Zeren/Automobile-PMR/LTspice/Input_mic_amplifier.asc

C1: cap; 10µ
C2: cap; 10µ
C3: cap; 10n
C4: cap; 10µ
C5: cap; 1n
C6: cap; 10n
C7: cap; 10n
C8: cap; 100n
R1: res; 1k
R2: res; 1k
R3: res; 10k
R4: res; 10k
R5: res; 10k
R6: res; 10k
R7: res; 10k
R8: res; 47k
R9: res; 47k
R10: res; 4.7k
R11: res; 4k7
R12: res; 4k7
R13: res; 4k7
R14: res; 4k7
R15: res; 47
U1: NE5532
U2: NE5532
U3: NE5532
V1: voltage; 15
V2: voltage; 7.5
V3: voltage; 0; AC 1; Rser=100
Named nets: 0, V+, REF, out
.ac dec 100 1 100meg
