Zeren/Automobile-PMR/LTspice/5x multiplier.asc

C1: cap; 10p
C2: cap; 1n
C3: cap; 12.734p
D1: schottky; RB715UM
L1: ind2; 318.354n
L2: ind2; 10n; Rser=0.1
R3: res; 1k
V1: voltage; PULSE(0 3.3 0 1n 1n 5.6053n 11.21n)
V2: voltage; 5; Rser=0
V3: voltage; SINE(1.65 1.65 89.2meg); AC 1; Rser=0
Named nets: 0
;ac dec 100 10meg 1g
.tran 1u
