Zeren/Automobile-PMR/LTspice/FM detector.asc

C1: cap; 100p
C2: cap; 120p
L1: ind; 1µ; Rser=1
R1: res; 10k
V1: voltage; SFFM(0 1 10.7meg 2 1k); AC 1
Named nets: 0, in, out
.tran 2m
