Zeren/Automobile-PMR/LTspice/AF amp.asc

C1: cap; 10n
C2: cap; 10.5n
C3: cap; 10n
C4: cap; 10.5n
C5: cap; 1µ
R1: res; 2.2k
R2: res; 9.1k
R3: res; 3k
R4: res; 2.4k
R5: res; 4.3k
R6: res; 4.7k
R7: res; 3k
R8: res; 2.4k
R9: res; 10k
U1: NE5532
U2: NE5532
V1: voltage; 5
V2: voltage; -5
V3: voltage; 1.6; AC 1
Named nets: v+, v-, 0, out
.ac dec 100 10 10meg
