Zeren/Automobile-PMR/LTspice/AGC detector.asc

C1: cap; 10n
C2: cap; 10n
C3: cap; 100n
D1: schottky; BAS40HM
L1: ind; 100µ
R1: res; 1800
R2: res; 50
R3: res; 50
R4: res; 10k
R5: res; 4k7
R6: res; 10k
R7: res; 10k
U1: LT1002
U2: LT1002
V1: voltage; SINE(0 0.5 10.7meg); AC 1
V2: voltage; 5
V3: voltage; -5
Named nets: 0, agc_out, rf_out, rf_in, det, tru, V+, V-
.tran 0 5m 4m
