Zeren/Automobile-PMR/LTspice/IF2 filter a amp.asc

C1: cap; 10n
C2: cap; 10n
C3: cap; 1n
C4: cap; 10n
C5: cap; 1µ
C6: cap; 1µ
C7: cap; 100n
R1: res; 10K
R2: res; 10K
R3: res; 50
R4: res; 10
R5: res; 100
R6: res; 10K
R7: res; 10K
R8: res; 10k
R9: res; 1k
R10: res; 1k
R11: res; 68k
U1: LM324
U2: LM324
U3: LM324
U5: LT1720
V1: voltage; 5
V2: voltage; -5
V3: voltage; SINE(0 2.23 100k); AC 1; Rser=50
V4: voltage; 1.6
V5: voltage; 3.3
Named nets: 0, V+, V-, in, out, REF
.tran 0.5m
;ac dec 100 1 100MEG
