Zeren/Automobile-PMR/Software/PMR_for_R124_V2/Core/Inc/rda1846.h

#ifndef RDA1846_H
#define RDA1846_H

#include "stm32g0xx_hal.h"

// I2C 7-bitová adresa (při SEN = Low)
#define RDA1846_I2C_ADDR  0x71

// Paging konstanty (stránkování nadadresových registrů)
#define RDA1846_PAGE_REG   0x7F
#define RDA1846_PAGE_UP    0x0001
#define RDA1846_PAGE_DOWN  0x0000
#define RDA1846_ADDR_LIMIT 0x80

// Využití unionu a bitfields pro bezpečnější přístup k registru 0x30
typedef union {
    uint16_t value;
    struct {
        uint16_t soft_reset   : 1;  // Bit 0
        uint16_t chip_cal_en  : 1;  // Bit 1
        uint16_t pdn_reg      : 1;  // Bit 2
        uint16_t sq_on        : 1;  // Bit 3
        uint16_t vox_on       : 1;  // Bit 4
        uint16_t rx_on        : 1;  // Bit 5
        uint16_t tx_on        : 1;  // Bit 6
        uint16_t mute         : 1;  // Bit 7
        uint16_t st_mode      : 2;  // Bity 9:8
        uint16_t reserved     : 1;  // Bit 10
        uint16_t tail_elim_en : 1;  // Bit 11
        uint16_t channel_mode : 2;  // Bity 13:12
        uint16_t others       : 2;  // Bity 15:14
    } bits;
} RDA1846_Reg30_t;

typedef struct {
    uint16_t tx_CTCSS;
    uint16_t rx_CTCSS;
    uint16_t tone;
} RDA1846_ctcss;

// RF Band Options
#define RDA1846_BAND_REG 0x0F
#define RDA1846_BAND_400_520MHZ  0x00
#define RDA1846_BAND_200_260MHZ  0x02
#define RDA1846_BAND_134_174MHZ  0x03

// Frequency setting
#define RDA1846_FREQ_HIGH_VALUE 0x29
#define RDA1846_FREQ_LOW_VALUE 0x2A

// Reference Clock Mode
#define RDA1846_CLOCK_XTAL_REG 0x2B
#define RDA1846_CLOCK_ADCLK_REG 0x2C
#define RDA1846_CLOCK_MODE_REG 0x04
#define RDA1846_CLOCK_MODE_12_14MHZ 0x0001
#define RDA1846_CLOCK_MODE_24_28MHZ 0x0000

//Deep sleep
#define RDA1846_DEEP_SLEEP_ENABLE 0x0004
#define RDA1846_DEEP_SLEEP_DISABLE 0x0000

//TX voice channel
#define RDA1846_TX_VOICE_CHANNEL_REG 0x3C
#define RDA1846_TX_VOICE_CHANNEL_MIC 0x0000
#define RDA1846_TX_VOICE_CHANNEL_TONE 0x4000
#define RDA1846_TX_VOICE_CHANNEL_GPIO1 0x8000
#define RDA1846_TX_VOICE_CHANNEL_NOSIGNAL 0xC000

//PA bias
#define RDA1846_PA_BIAX_REG 0x0A

//Subaudio
#define RDA1846_CTCSS_CDCSS_MODE_REG 0x45
#define RDA1846_CTCSS_INNER_CTCSS_EN 0x0001
#define RDA1846_CTCSS_INNER_CDCSS_EN 0x0002
#define RDA1846_CTCSS_OUTTER_CTCSS_EN 0x0005
#define RDA1846_CTCSS_OUTTER_CDCSS_EN 0x0006

#define RDA1846_CTCSS_FREQ_REG 0x4A

// RDA1846 Flags
#define FLAG_SQUELCH_OPEN      (1 << 0)
#define FLAG_CTCSS_DETECTED    (1 << 1)
#define FLAG_DCS_DETECTED      (1 << 2)
#define FLAG_RX_ACTIVE         (1 << 3)
#define FLAG_TX_ACTIVE         (1 << 4)
#define FLAG_LOW_VOLTAGE       (1 << 5)
#define FLAG_PLL_LOCK          (1 << 6)
#define FLAG_RSSI_HIGH         (1 << 7)
// Správné adresy stavových registrů
#define RDA1846_FLAG_REG 0x5C
#define RDA1846_RSSI_REG 0x5F
#define RDA1846_VSSI_REG 0x60

// Správné mapování bitů v registru 0x5C (Flag)
#define FLAG_VOX               (1 << 0)
#define FLAG_SQUELCH_OPEN      (1 << 1)
#define FLAG_CTCSS_DETECTED    (1 << 2)
#define FLAG_INVERT_DET        (1 << 7)
#define FLAG_TXON_RF           (1 << 9)
#define FLAG_RXON_RF           (1 << 10)
#define FLAG_DTMF_IDLE         (1 << 12)
// ---------------------------------------------------------
// EXTERN DEKLARACE PRO SDÍLENÍ MEZI MODULY
// ---------------------------------------------------------
extern const uint32_t PMR446_Frequencies[16];
extern const uint16_t CTCSS_Tones[39];

// Global UART Handle
extern UART_HandleTypeDef huart2;
extern I2C_HandleTypeDef hi2c1;

void RDA1846_Init(void);
HAL_StatusTypeDef RDA1846_WriteRegister(uint16_t reg, uint16_t value);
uint16_t RDA1846_ReadRegister(uint8_t reg);
void RDA1846_SetFrequency(uint32_t freq);
void RDA1846_SetReferenceClock(uint16_t clock_frequency);
void RDA1846_SetTxMode(RDA1846_Reg30_t *settings, RDA1846_ctcss *ctcss);
void RDA1846_SetRxMode(RDA1846_Reg30_t *settings, RDA1846_ctcss *ctcss);
void RDA1846_Set_Reg_0x30(RDA1846_Reg30_t *settings);
void RDA1846_SetTxVoiceChannel(uint8_t channel);
void RDA1846_SetTxPaBias(uint16_t bias);
void RDA1846_SetCTCSS_FREQ(RDA1846_ctcss *ctcss, uint16_t freq_10th_hz);
void RDA1846_SetCTCSS_TONE(RDA1846_ctcss *ctcss);
uint16_t RDA1846_ReadRSSI(void);
uint16_t RDA1846_ReadVSSI(void);
uint16_t RDA1846_ReadFlags(void);
void RDA1846_SendFlagsUART_DMA(uint16_t flags);
void RDA1846_SetSquelchThresholds(int8_t open_dbm, int8_t shut_dbm);

#endif // RDA1846_H
