Zeren/Automobile-PMR/Software/LMX2572_test/main.py

import time

import spidev

registers = [0x7D2288,
             0x7C0000,
             0x7B0000,
             0x7A0000,
             0x790000,
             0x780000,
             0x770000,
             0x760000,
             0x750000,
             0x740000,
             0x730000,
             0x727802,
             0x710000,
             0x700000,
             0x6F0000,
             0x6E0000,
             0x6D0000,
             0x6C0000,
             0x6B0000,
             0x6A0007,
             0x694440,
             0x682710,
             0x670000,
             0x660000,
             0x650000,
             0x642710,
             0x630000,
             0x620000,
             0x610000,
             0x600000,
             0x5F0000,
             0x5E0000,
             0x5D0000,
             0x5C0000,
             0x5B0000,
             0x5A0000,
             0x590000,
             0x580000,
             0x570000,
             0x560000,
             0x55D800,
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


def reset(spi) -> None:
    setup_data = [0x00, 0b00100011, 0b00011110]
    spi.writebytes(setup_data)
    time.sleep(0.01)


def testovaci_stusteni(spi) -> None:
    # VCO kalibrace
    data = [78, 0x02, 0b00110011]
    spi.writebytes(data)

    # Vystupni divider CHDIV = 5 => outDIB = 16 => Fout = 3500/16=218MHz
    data = [75, 0x01, 0b01000000]
    spi.writebytes(data)

    # Musi se to po resetu preprogramovat
    data = [71, 0x00, 0x81]
    spi.writebytes(data)

    # Musi se to po resetu preprogramovat
    data = [57, 0x00, 0x20]
    spi.writebytes(data)

    # Musi se to po resetu preprogramovat
    data = [52, 0x04, 0x21]
    spi.writebytes(data)

    # PLL_N nastavit na VCO 3.5GHz => N =  35
    data = [36, 0x00, 35]
    spi.writebytes(data)
    data = [34, 0x00, 0x10]
    spi.writebytes(data)

    # Musi se to po resetu preprogramovat
    data = [30, 0x0c, 0xa6]
    spi.writebytes(data)

    # Musi se to po resetu preprogramovat
    data = [29, 0, 0]
    spi.writebytes(data)

    # PLL_R = 1
    data = [11, 0b10110000, 0b00001000]
    spi.writebytes(data)

    # MULT = 4
    data = [10, 16 + 4, 0x78]
    spi.writebytes(data)

    # diff vystup, zakonceny 100 ohm
    data = [5, 0b00101000, 0xc8]
    spi.writebytes(data)

    # Reg 0
    data = [0, 0b00100001, 0b00011100]
    spi.writebytes(data)


def main() -> None:
    spi = spidev.SpiDev()
    spi.open(0, 0)
    spi.max_speed_hz = 10000000
    spi.mode = 0  # TOHLE JE DOLEZITE
    reset(spi)

    for zapis in registers:
        data = [zapis >> 16 & 255, zapis >> 8 & 255, zapis & 255]
        spi.writebytes(data)
        print(data)


if __name__ == '__main__':
    main()

# See PyCharm help at https://www.jetbrains.com/help/pycharm/
